freeDSP/freeDSP-CLASSIC-SMD-B/Simulations/Filter/Messungen OPA1662/NewFile0.bmp

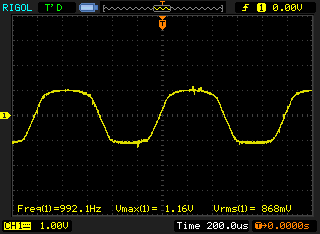
Simulations/Filter/Messungen OPA1662/NewFile0.bmp
