freeDSP/freeDSP-CLASSIC-SMD-B/Simulations/muting/measurements/inverter_freq_voltage.bmp

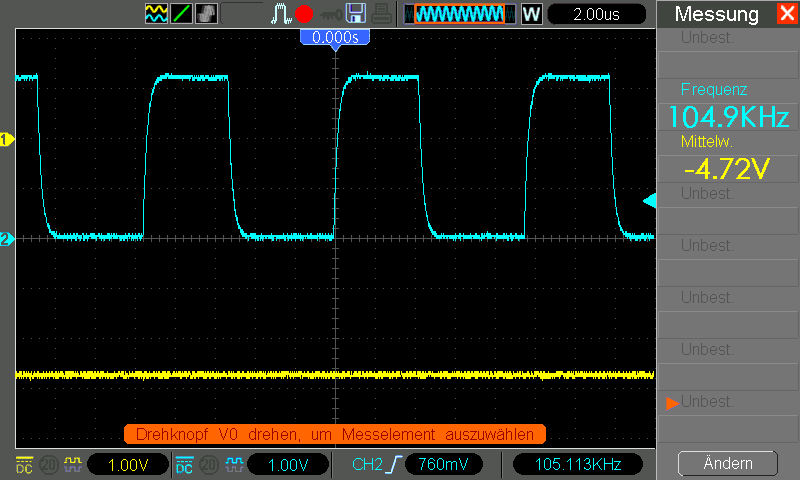
Simulations/muting/measurements/inverter_freq_voltage.bmp
