freeDSP/freeDSP-CLASSIC-SMD-B/Simulations/muting/inverter.asc

A1: schmtinv; vhigh=3.3 ref=1.5 Trise=5n Tfall=5n Td=5n
A2: schmtinv; vhigh=3.3 ref=1.5 Trise=5n Tfall=5n Td=5n
A3: schmtinv; vhigh=3.3 ref=1.5 Trise=5n Tfall=5n Td=5n
C1: cap; 100n
C2: cap; 100n
C3: cap; 100n
C4: cap; 100n
C5: cap; 10n
D1: diode; 1N4148
D2: diode; 1N4148
D3: diode; 1N4148
D4: diode; 1N4148
R1: res; 1k
R2: res; 5meg
R3: res; 1k
Named nets: 0
.tran 0 220u 200u 1u uic
Inverter sind SN74LVC3G14
f_s (gemessen) = 105kHz
