freeDSP/freeDSP-CLASSIC-SMD-B/Simulations/muting/muting.asc

C1: cap; 10µ
J1: njf; PN5434
M1: nmos; BSH103
M4: nmos; BSH103
R1: res; 10k
V1: voltage; PULSE(0 1.65 1m 5u)
V2: voltage; PULSE(0 -4 5m 5n 5n 5m)
V3: voltage; PULSE(0 3.3 5m 100u 5n 5m)
V4: voltage; SINE(1.65 1.27 1k 0 0 0)
Named nets: 0
.tran 0 10m 0 10n
.include BSH103.mod
.four 1k 10 10 v(n005)
Muting mit 0V an allen Gates, Unmuting mit 3.3V an den MOSFETs und <-4V am JFET
.include PN5434.mod
PN5434 ist abgekündigt, Ersatztyp ist MMBF5434
