freeDSP/freeDSP-CLASSIC-SMD-B/Simulations/muting/trigger.asc

C1: cap; 2.2µ
D2: diode; 1N4148
R1: res; 10k
R2: res; 10k
R3: res; 390k
R4: res; 1k
R5: res; 1meg
R6: res; 1k
U1: opamp2; LM339
V1: voltage; PULSE(0 3.3 0 5n 5n 1 1.1)
Named nets: 0, OUT
.tran 0 8 0 10u startup
Schaltet real bei ca. 500ms
.include LM339.lib
Komparator wird später ein LM393 verwendet (gleiches Verhalten wie LM339)
