freeDSP/freeDSP-CLASSIC-SMD-B/Simulations/Filter/120kHz Grenzfrequenz/120kHz.asc

C1: cap; 100p
C2: cap; 330p
C3: cap; 4.7µ
C4: cap; 4.7µ
C5: cap; 560p
R1: res; 2k
R2: res; 16k
R3: res; 2.4k
R4: res; 10k
U1: opamp2; OPA388
V1: voltage; 1.65; AC 1.27 0
V2: voltage; 3.3
V3: voltage; 3.3
Named nets: 0, V+, V-
.LIB OPA4353.lib
.LIB ad8608.cir
.ac dec 1000 1 100G
.LIB OPA1662.lib
.LIB lme49721.lib
.LIB OPA1664.lib
.LIB OPA388.txt
