freeDSP/freeDSP-CLASSIC-SMD-B/SOURCES/freeDSP_Classic_SMD.kicad_pcb

## KiCad design SOURCES/freeDSP_Classic_SMD.kicad_pcb (2019-07-08)

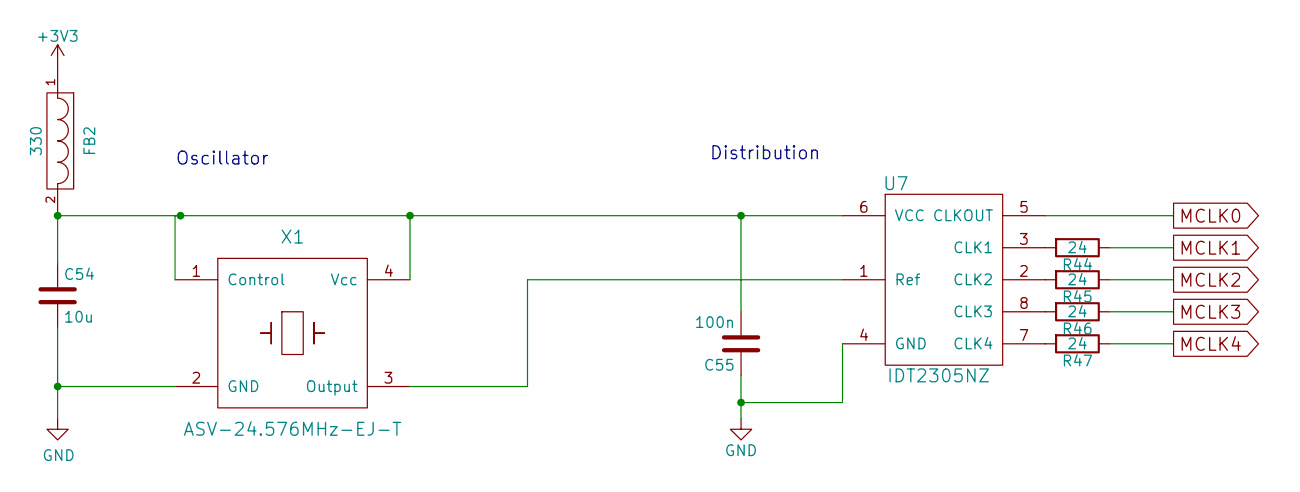
[picture p16: schematic clock-2019-01-28-18-36-09.sch, Clock]

Parts:
C54: 10u; C_1206_HandSoldering
C55: 100n; C_1206_HandSoldering
FB2: 330; C_0805_HandSoldering
R44, R45, R46, R47: 24; R_1206_HandSoldering
U7: IDT2305NZ; SOIC-8_3.9x4.9mm_Pitch1.27mm
X1: ASV-24.576MHz-EJ-T; Oscillator_SMD_Abracon_ASV-4pin_7.0x5.1mm_HandSoldering

Connections:
GND: C54.2, C55.1, U7.4 (GND), X1.2 (GND); also elsewhere on the board
MCLK0: U7.5 (CLKOUT); also elsewhere on the board
MCLK1: R44.1; also elsewhere on the board
MCLK2: R45.1; also elsewhere on the board
MCLK3: R46.1; also elsewhere on the board
MCLK4: R47.1; also elsewhere on the board
unnamed: C54.1, C55.2, FB2.2, U7.6 (VCC), X1.1 (Control), X1.4 (Vcc)
unnamed: R44.2, U7.3 (CLK1)
unnamed: R45.2, U7.2 (CLK2)
unnamed: R46.2, U7.8 (CLK3)
unnamed: R47.2, U7.7 (CLK4)
unnamed: U7.1 (Ref), X1.3 (Output)

Notes on the sheet:
Oscillator
Distribution


Parts:
C54: 10u; C_1206_HandSoldering
C55: 100n; C_1206_HandSoldering
FB2: 330; C_0805_HandSoldering
R44, R45, R46, R47: 24; R_1206_HandSoldering
U7: IDT2305NZ; SOIC-8_3.9x4.9mm_Pitch1.27mm
X1: ASV-24.576MHz-EJ-T; Oscillator_SMD_Abracon_ASV-4pin_7.0x5.1mm_HandSoldering

Connections:
GND: C54.2, C55.1, U7.4 (GND), X1.2 (GND); also elsewhere on the board
MCLK0: U7.5 (CLKOUT); also elsewhere on the board
MCLK1: R44.1; also elsewhere on the board
MCLK2: R45.1; also elsewhere on the board
MCLK3: R46.1; also elsewhere on the board
MCLK4: R47.1; also elsewhere on the board
unnamed: C54.1, C55.2, FB2.2, U7.6 (VCC), X1.1 (Control), X1.4 (Vcc)
unnamed: R44.2, U7.3 (CLK1)
unnamed: R45.2, U7.2 (CLK2)
unnamed: R46.2, U7.8 (CLK3)
unnamed: R47.2, U7.7 (CLK4)
unnamed: U7.1 (Ref), X1.3 (Output)

Notes on the sheet:
Oscillator
Distribution


Parts:
C54: 10u; C_1206_HandSoldering
C55: 100n; C_1206_HandSoldering
FB2: 330; C_0805_HandSoldering
R44, R45, R46, R47: 24; R_1206_HandSoldering
U7: IDT2305NZ; SOIC-8_3.9x4.9mm_Pitch1.27mm
X1: ASV-24.576MHz-EJ-T; Oscillator_SMD_Abracon_ASV-4pin_7.0x5.1mm_HandSoldering

Connections:
GND: C54.2, C55.1, U7.4 (GND), X1.2 (GND); also elsewhere on the board
MCLK0: U7.5 (CLKOUT); also elsewhere on the board
MCLK1: R44.1; also elsewhere on the board
MCLK2: R45.1; also elsewhere on the board
MCLK3: R46.1; also elsewhere on the board
MCLK4: R47.1; also elsewhere on the board
unnamed: C54.1, C55.2, FB2.2, U7.6 (VCC), X1.1 (Control), X1.4 (Vcc)
unnamed: R44.2, U7.3 (CLK1)
unnamed: R45.2, U7.2 (CLK2)
unnamed: R46.2, U7.8 (CLK3)
unnamed: R47.2, U7.7 (CLK4)
unnamed: U7.1 (Ref), X1.3 (Output)

Notes on the sheet:
Oscillator
Distribution

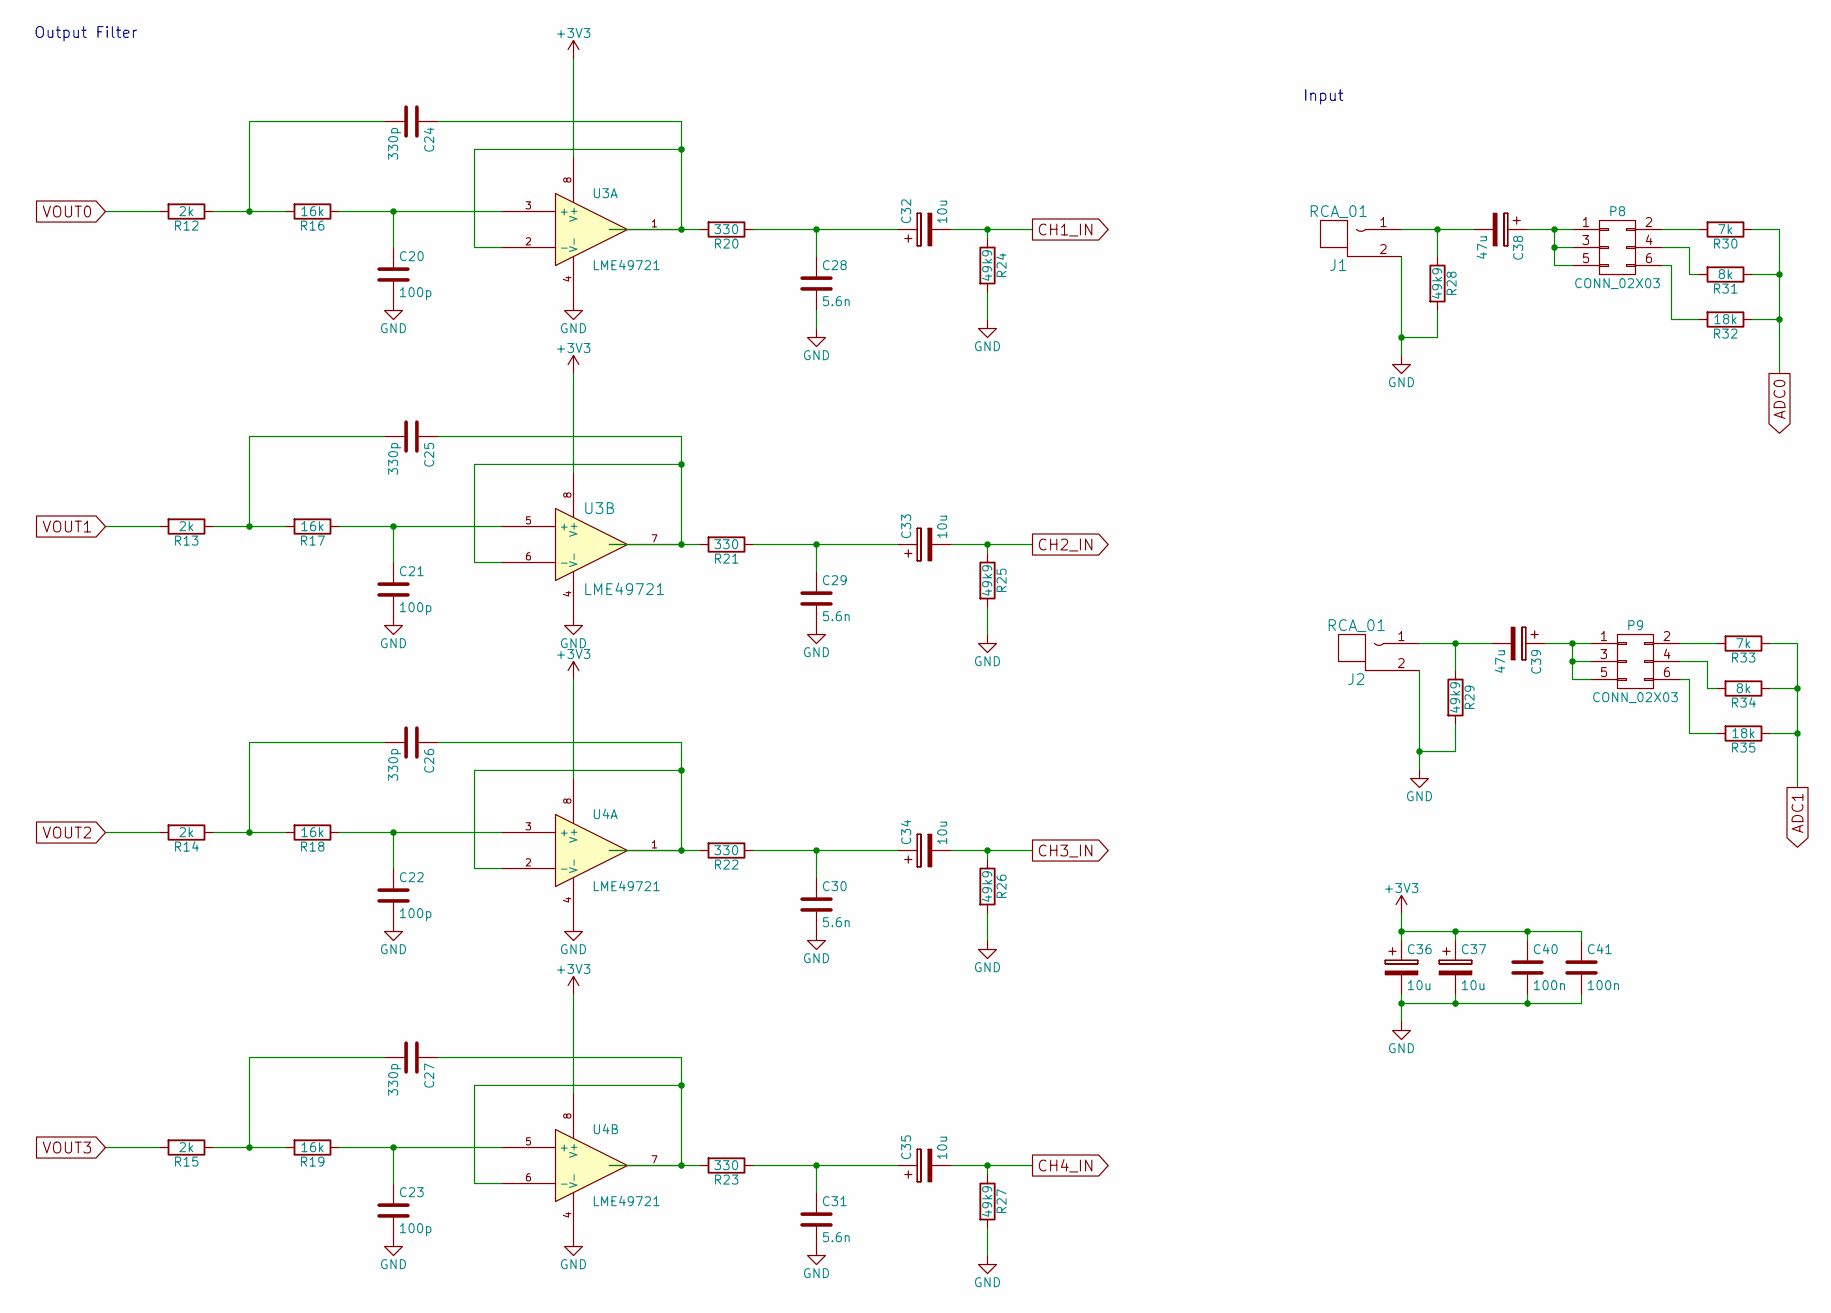
[picture p17: schematic filter-2019-01-28-18-36-09.sch, Filter]

Parts:
C20, C21, C22, C23: 100p; C_1206_HandSoldering
C24, C25, C26, C27: 330p; C_1206_HandSoldering
C28, C29, C30, C31: 5.6n; C_1206_HandSoldering
C32, C33, C34, C35, C36, C37: 10u; C_Radial_D5_L11_P2
C38, C39: 47u; C_Radial_D5_L11_P2
C40, C41: 100n; C_1206_HandSoldering
J1, J2: RCA_01; RCA_RCJ-01x
P8, P9: CONN_02X03; Pin_Header_Straight_2x03
R12, R13, R14, R15: 2k; R_1206_HandSoldering
R16, R17, R18, R19: 16k; R_1206_HandSoldering
R20, R21, R22, R23: 330; R_1206_HandSoldering
R24, R25, R26, R27, R28, R29: 49k9; R_1206_HandSoldering
R30, R33: 7k; R_1206_HandSoldering
R31, R34: 8k; R_1206_HandSoldering
R32, R35: 18k; R_1206_HandSoldering
U3, U4: LME49721; SOIC-8_3.9x4.9mm_Pitch1.27mm

Connections:
ADC0: R30.1, R31.1, R32.1; also elsewhere on the board
ADC1: R33.1, R34.1, R35.1; also elsewhere on the board
CH1_IN: C32.2, R24.1; also elsewhere on the board
CH2_IN: C33.2, R25.1; also elsewhere on the board
CH3_IN: C34.2, R26.1; also elsewhere on the board
CH4_IN: C35.2, R27.1; also elsewhere on the board
GND: C20.2, C21.2, C22.2, C23.2, C28.2, C29.2, C30.2, C31.2, C36.2, C37.2, C40.2, C41.2, J1.2 (GND), J2.2 (GND), R24.2, R25.2, R26.2, R27.2, R28.2, R29.2, U3.4 (V-), U4.4 (V-); also elsewhere on the board
unnamed: C20.1, R16.1, U3.3 (+)
unnamed: C21.1, R17.1, U3.5 (+)
unnamed: C22.1, R18.1, U4.3 (+)
unnamed: C23.1, R19.1, U4.5 (+)
unnamed: C24.1, R20.2, U3.1, U3.2 (-)
unnamed: C24.2, R12.1, R16.2
unnamed: C25.1, R21.2, U3.6 (-), U3.7
unnamed: C25.2, R13.1, R17.2
unnamed: C26.1, R22.2, U4.1, U4.2 (-)
unnamed: C26.2, R14.1, R18.2
unnamed: C27.1, R23.2, U4.6 (-), U4.7
unnamed: C27.2, R15.1, R19.2
unnamed: C28.1, C32.1, R20.1
unnamed: C29.1, C33.1, R21.1
unnamed: C30.1, C34.1, R22.1
unnamed: C31.1, C35.1, R23.1
unnamed: C38.1, P8.1, P8.3, P8.5
unnamed: C38.2, J1.1 (SIG), R28.1
unnamed: C39.1, P9.1, P9.3, P9.5
unnamed: C39.2, J2.1 (SIG), R29.1
unnamed: P8.2, R30.2
unnamed: P8.4, R31.2
unnamed: P8.6, R32.2
unnamed: P9.2, R33.2
unnamed: P9.4, R34.2
unnamed: P9.6, R35.2
VOUT0: R12.2; also elsewhere on the board
VOUT1: R13.2; also elsewhere on the board
VOUT2: R14.2; also elsewhere on the board
VOUT3: R15.2; also elsewhere on the board

Notes on the sheet:
Output Filter
Input


Parts:
C20, C21, C22, C23: 100p; C_1206_HandSoldering
C24, C25, C26, C27: 330p; C_1206_HandSoldering
C28, C29, C30, C31: 5.6n; C_1206_HandSoldering
C32, C33, C34, C35, C36, C37: 10u; C_Radial_D5_L11_P2
C38, C39: 47u; C_Radial_D5_L11_P2
C40, C41: 100n; C_1206_HandSoldering
J1, J2: RCA_01; RCA_RCJ-01x
P8, P9: CONN_02X03; Pin_Header_Straight_2x03
R12, R13, R14, R15: 2k; R_1206_HandSoldering
R16, R17, R18, R19: 16k; R_1206_HandSoldering
R20, R21, R22, R23: 330; R_1206_HandSoldering
R24, R25, R26, R27, R28, R29: 49k9; R_1206_HandSoldering
R30, R33: 7k; R_1206_HandSoldering
R31, R34: 8k; R_1206_HandSoldering
R32, R35: 18k; R_1206_HandSoldering
U3, U4: LME49721; SOIC-8_3.9x4.9mm_Pitch1.27mm

Connections:
ADC0: R30.1, R31.1, R32.1; also elsewhere on the board
ADC1: R33.1, R34.1, R35.1; also elsewhere on the board
CH1_IN: C32.2, R24.1; also elsewhere on the board
CH2_IN: C33.2, R25.1; also elsewhere on the board
CH3_IN: C34.2, R26.1; also elsewhere on the board
CH4_IN: C35.2, R27.1; also elsewhere on the board
GND: C20.2, C21.2, C22.2, C23.2, C28.2, C29.2, C30.2, C31.2, C36.2, C37.2, C40.2, C41.2, J1.2 (GND), J2.2 (GND), R24.2, R25.2, R26.2, R27.2, R28.2, R29.2, U3.4 (V-), U4.4 (V-); also elsewhere on the board
unnamed: C20.1, R16.1, U3.3 (+)
unnamed: C21.1, R17.1, U3.5 (+)
unnamed: C22.1, R18.1, U4.3 (+)
unnamed: C23.1, R19.1, U4.5 (+)
unnamed: C24.1, R20.2, U3.1, U3.2 (-)
unnamed: C24.2, R12.1, R16.2
unnamed: C25.1, R21.2, U3.6 (-), U3.7
unnamed: C25.2, R13.1, R17.2
unnamed: C26.1, R22.2, U4.1, U4.2 (-)
unnamed: C26.2, R14.1, R18.2
unnamed: C27.1, R23.2, U4.6 (-), U4.7
unnamed: C27.2, R15.1, R19.2
unnamed: C28.1, C32.1, R20.1
unnamed: C29.1, C33.1, R21.1
unnamed: C30.1, C34.1, R22.1
unnamed: C31.1, C35.1, R23.1
unnamed: C38.1, P8.1, P8.3, P8.5
unnamed: C38.2, J1.1 (SIG), R28.1
unnamed: C39.1, P9.1, P9.3, P9.5
unnamed: C39.2, J2.1 (SIG), R29.1
unnamed: P8.2, R30.2
unnamed: P8.4, R31.2
unnamed: P8.6, R32.2
unnamed: P9.2, R33.2
unnamed: P9.4, R34.2
unnamed: P9.6, R35.2
VOUT0: R12.2; also elsewhere on the board
VOUT1: R13.2; also elsewhere on the board
VOUT2: R14.2; also elsewhere on the board
VOUT3: R15.2; also elsewhere on the board

Notes on the sheet:
Output Filter
Input


Parts:
C20, C21, C22, C23: 100p; C_1206_HandSoldering
C24, C25, C26, C27: 330p; C_1206_HandSoldering
C28, C29, C30, C31: 5.6n; C_1206_HandSoldering
C32, C33, C34, C35, C36, C37: 10u; C_Radial_D5_L11_P2
C38, C39: 47u; C_Radial_D5_L11_P2
C40, C41: 100n; C_1206_HandSoldering
J1, J2: RCA_01; RCA_RCJ-01x
P8, P9: CONN_02X03; Pin_Header_Straight_2x03
R12, R13, R14, R15: 2k; R_1206_HandSoldering
R16, R17, R18, R19: 16k; R_1206_HandSoldering
R20, R21, R22, R23: 330; R_1206_HandSoldering
R24, R25, R26, R27, R28, R29: 49k9; R_1206_HandSoldering
R30, R33: 7k; R_1206_HandSoldering
R31, R34: 8k; R_1206_HandSoldering
R32, R35: 18k; R_1206_HandSoldering
U3, U4: LME49721; SOIC-8_3.9x4.9mm_Pitch1.27mm

Connections:
ADC0: R30.1, R31.1, R32.1; also elsewhere on the board
ADC1: R33.1, R34.1, R35.1; also elsewhere on the board
CH1_IN: C32.2, R24.1; also elsewhere on the board
CH2_IN: C33.2, R25.1; also elsewhere on the board
CH3_IN: C34.2, R26.1; also elsewhere on the board
CH4_IN: C35.2, R27.1; also elsewhere on the board
GND: C20.2, C21.2, C22.2, C23.2, C28.2, C29.2, C30.2, C31.2, C36.2, C37.2, C40.2, C41.2, J1.2 (GND), J2.2 (GND), R24.2, R25.2, R26.2, R27.2, R28.2, R29.2, U3.4 (V-), U4.4 (V-); also elsewhere on the board
unnamed: C20.1, R16.1, U3.3 (+)
unnamed: C21.1, R17.1, U3.5 (+)
unnamed: C22.1, R18.1, U4.3 (+)
unnamed: C23.1, R19.1, U4.5 (+)
unnamed: C24.1, R20.2, U3.1, U3.2 (-)
unnamed: C24.2, R12.1, R16.2
unnamed: C25.1, R21.2, U3.6 (-), U3.7
unnamed: C25.2, R13.1, R17.2
unnamed: C26.1, R22.2, U4.1, U4.2 (-)
unnamed: C26.2, R14.1, R18.2
unnamed: C27.1, R23.2, U4.6 (-), U4.7
unnamed: C27.2, R15.1, R19.2
unnamed: C28.1, C32.1, R20.1
unnamed: C29.1, C33.1, R21.1
unnamed: C30.1, C34.1, R22.1
unnamed: C31.1, C35.1, R23.1
unnamed: C38.1, P8.1, P8.3, P8.5
unnamed: C38.2, J1.1 (SIG), R28.1
unnamed: C39.1, P9.1, P9.3, P9.5
unnamed: C39.2, J2.1 (SIG), R29.1
unnamed: P8.2, R30.2
unnamed: P8.4, R31.2
unnamed: P8.6, R32.2
unnamed: P9.2, R33.2
unnamed: P9.4, R34.2
unnamed: P9.6, R35.2
VOUT0: R12.2; also elsewhere on the board
VOUT1: R13.2; also elsewhere on the board
VOUT2: R14.2; also elsewhere on the board
VOUT3: R15.2; also elsewhere on the board

Notes on the sheet:
Output Filter
Input

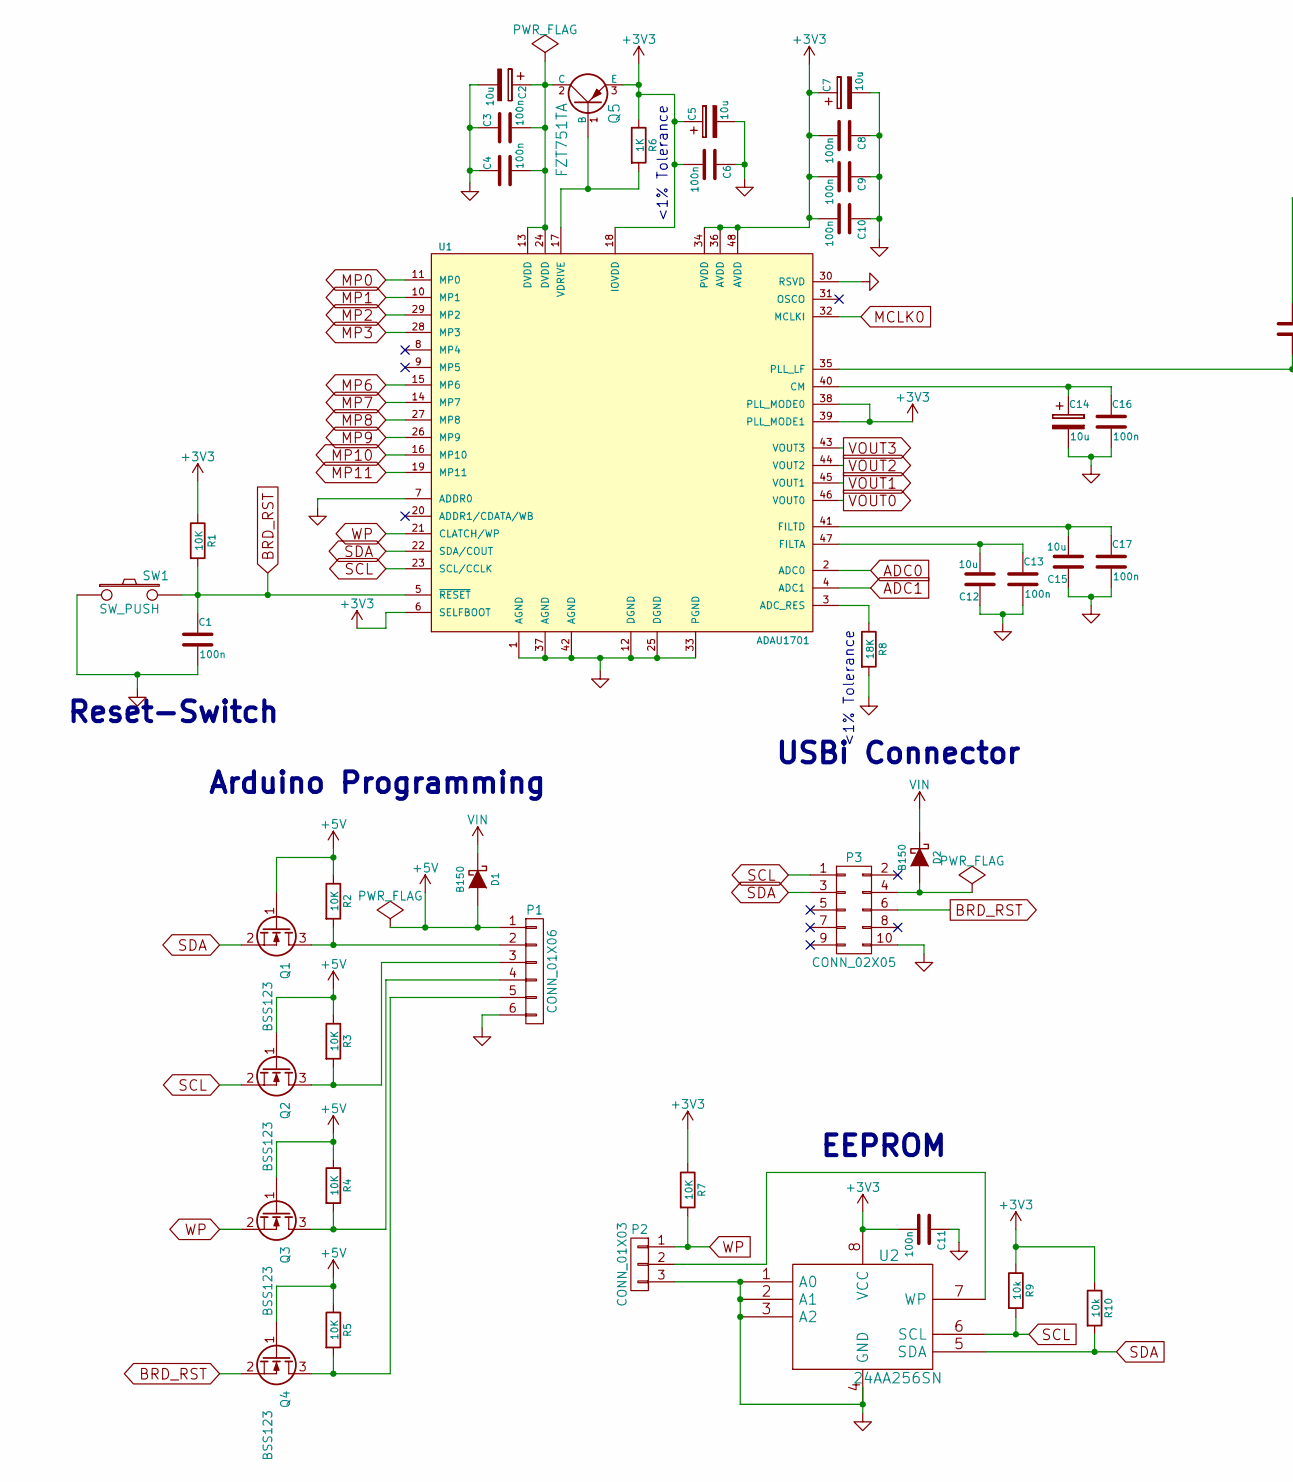
[picture p18: schematic freeDSP_Classic_SMD-2019-01-28-18-36-09.sch, freeDSP Classic SMD, part in row 1, column 1]

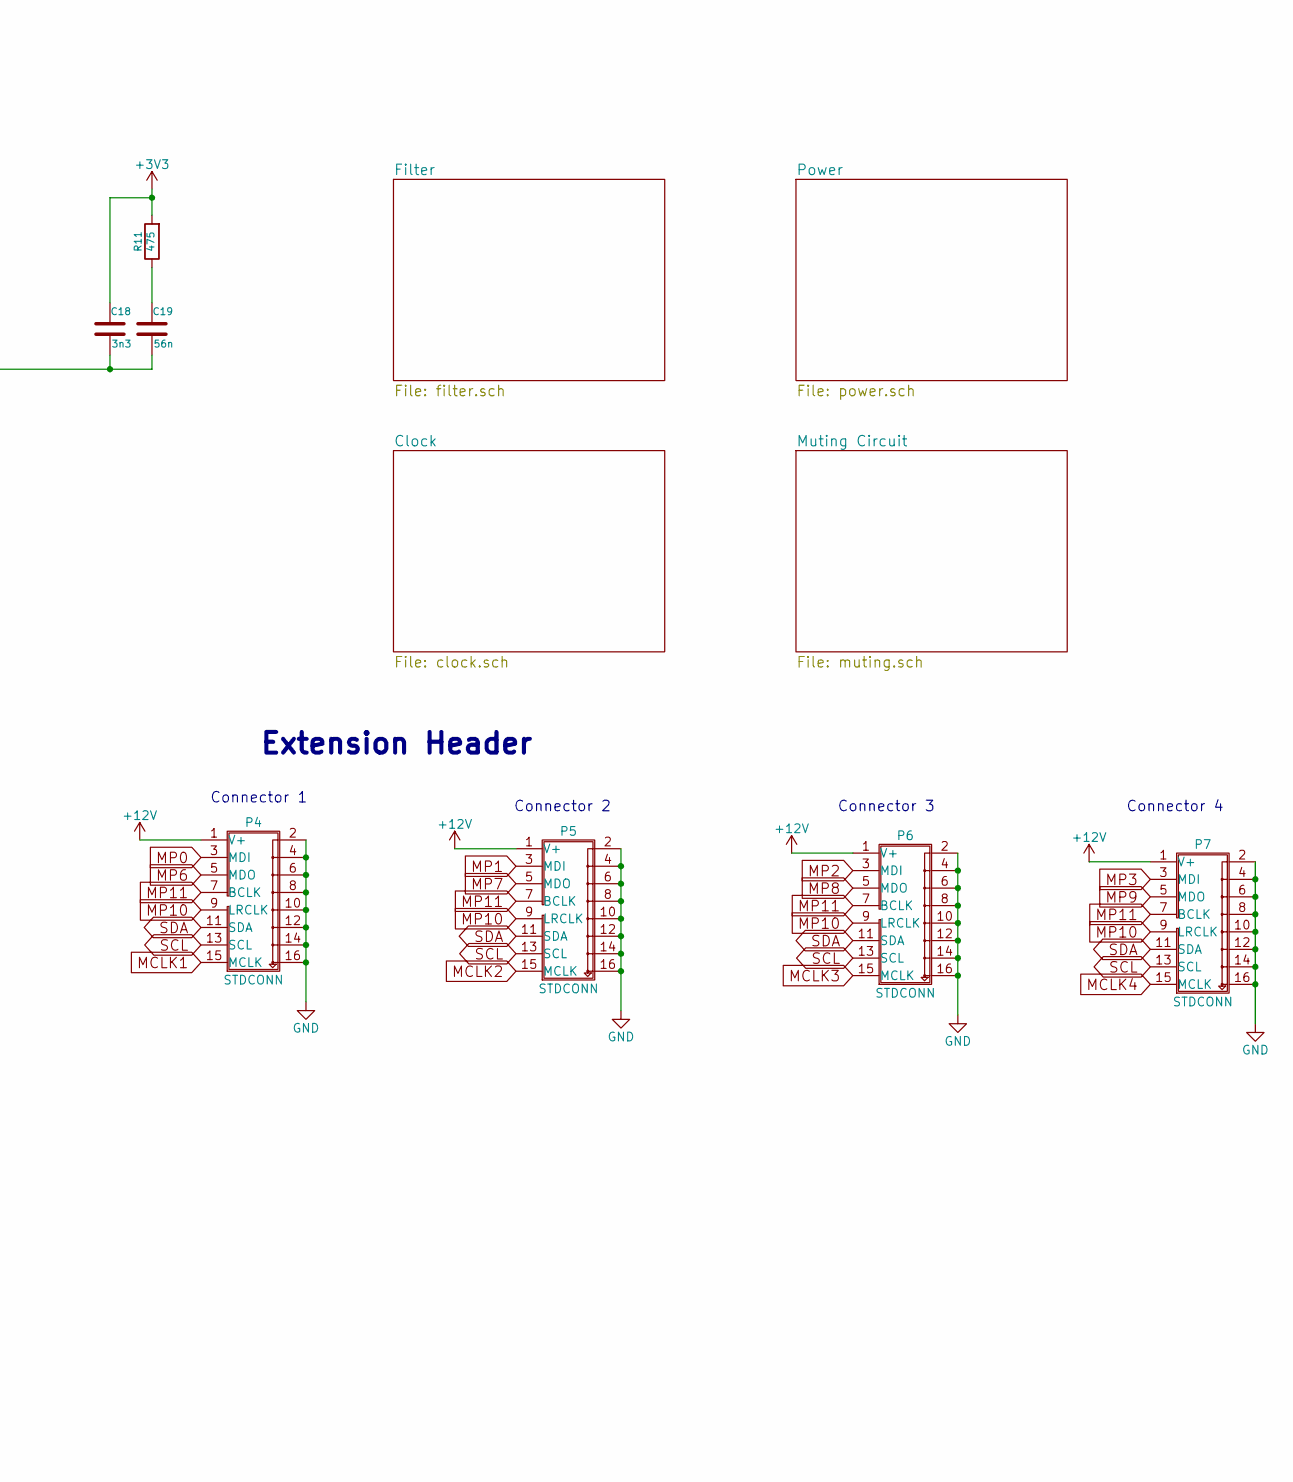
[picture p19: schematic freeDSP_Classic_SMD-2019-01-28-18-36-09.sch, freeDSP Classic SMD, part in row 1, column 2]

Parts:
C1, C3, C4, C6, C8, C9, C10, C11, C13, C16, C17: 100n; C_1206_HandSoldering
C2, C5, C7, C14: 10u; C_Radial_D5_L11_P2
C12, C15: 10u; C_1206_HandSoldering
C18: 3n3; C_1206_HandSoldering
C19: 56n; C_1206_HandSoldering
D1, D2: B150; SMA
P1: CONN_01X06; Pin_Header_Straight_1x06
P2: CONN_01X03; Pin_Header_Straight_1x03
P3: CONN_02X05; IDC_Header_Straight_10pins
P4, P5, P6, P7: STDCONN; IDC_Header_Straight_16pins
Q1, Q2, Q3, Q4: BSS123; SOT-23_Handsoldering
Q5: FZT751TA; SOT-223
R1, R2, R3, R4, R5, R7: 10K; R_1206_HandSoldering
R6: 1K; R_1206_HandSoldering
R8: 18K; R_1206_HandSoldering
R9, R10: 10k; R_1206_HandSoldering
R11: 475; R_1206_HandSoldering
SW1: SW_PUSH; SW_PUSH_6mm
U1: ADAU1701; LQFP-48_7x7mm_Pitch0.5mm
U2: 24AA256SN; SOIC-8_3.9x4.9mm_Pitch1.27mm

Connections:
+5V: D1.2 (A), P1.1, Q1.1 (G), Q2.1 (G), Q3.1 (G), Q4.1 (G), R2.1, R3.1, R4.1, R5.1
+12V: P4.1 (V+), P5.1 (V+), P6.1 (V+), P7.1 (V+); also elsewhere on the board
ADC0: U1.2 (ADC0); also elsewhere on the board
ADC1: U1.4 (ADC1); also elsewhere on the board
BRD_RST: C1.1, P3.6, Q4.2 (S), R1.2, SW1.2, U1.5 (~RESET~)
GND: C1.2, C2.2, C3.1, C4.1, C5.2, C6.1, C7.2, C8.1, C9.1, C10.1, C11.1, C12.1, C13.2, C14.2, C15.1, C16.2, C17.2, P1.6, P2.3, P3.10, P4.2 (GND), P4.4 (GND), P4.6 (GND), P4.8 (GND), P4.10 (GND), P4.12 (GND), P4.14 (GND), P4.16 (GND), P5.2 (GND), P5.4 (GND), P5.6 (GND), P5.8 (GND), P5.10 (GND), P5.12 (GND), P5.14 (GND), P5.16 (GND), P6.2 (GND), P6.4 (GND), P6.6 (GND), P6.8 (GND), P6.10 (GND), P6.12 (GND), P6.14 (GND), P6.16 (GND), P7.2 (GND), P7.4 (GND), P7.6 (GND), P7.8 (GND), P7.10 (GND), P7.12 (GND), P7.14 (GND), P7.16 (GND), R8.2, SW1.1, U1.1 (AGND), U1.7 (ADDR0), U1.12 (DGND), U1.25 (DGND), U1.30 (RSVD), U1.33 (PGND), U1.37 (AGND), U1.42 (AGND), U2.1 (A0), U2.2 (A1), U2.3 (A2), U2.4 (GND); also elsewhere on the board
MCLK0: U1.32 (MCLKI); also elsewhere on the board
MCLK1: P4.15 (MCLK); also elsewhere on the board
MCLK2: P5.15 (MCLK); also elsewhere on the board
MCLK3: P6.15 (MCLK); also elsewhere on the board
MCLK4: P7.15 (MCLK); also elsewhere on the board
MP0: P4.3 (MDI), U1.11 (MP0)
MP1: P5.3 (MDI), U1.10 (MP1)
MP2: P6.3 (MDI), U1.29 (MP2)
MP3: P7.3 (MDI), U1.28 (MP3)
MP4: U1.8 (MP4); also elsewhere on the board
MP5: U1.9 (MP5); also elsewhere on the board
MP6: P4.5 (MDO), U1.15 (MP6)
MP7: P5.5 (MDO), U1.14 (MP7)
MP8: P6.5 (MDO), U1.27 (MP8)
MP9: P7.5 (MDO), U1.26 (MP9)
unnamed: C2.1, C3.2, C4.2, Q5.2 (C), U1.13 (DVDD), U1.24 (DVDD)
unnamed: C12.2, C13.1, U1.47 (FILTA)
unnamed: C14.1, C16.1, U1.40 (CM)
unnamed: C15.2, C17.1, U1.41 (FILTD)
unnamed: C18.2, C19.2, U1.35 (PLL_LF)
unnamed: C19.1, R11.1
unnamed: D2.2 (A), P3.4
unnamed: P1.2, Q1.3 (D), R2.2
unnamed: P1.3, Q2.3 (D), R3.2
unnamed: P1.4, Q3.3 (D), R4.2
unnamed: P1.5, Q4.3 (D), R5.2
unnamed: P2.2, U2.7 (WP)
unnamed: Q5.1 (B), R6.2, U1.17 (VDRIVE)
unnamed: R8.1, U1.3 (ADC_RES)
SCL: P3.1, P4.13 (SCL), P5.13 (SCL), P6.13 (SCL), P7.13 (SCL), Q2.2 (S), R9.2, U1.23 (SCL/CCLK), U2.6 (SCL)
SDA: P3.3, P4.11 (SDA), P5.11 (SDA), P6.11 (SDA), P7.11 (SDA), Q1.2 (S), R10.2, U1.22 (SDA/COUT), U2.5 (SDA)
VIN: D1.1 (K), D2.1 (K); also elsewhere on the board
VOUT0: U1.46 (VOUT0); also elsewhere on the board
VOUT1: U1.45 (VOUT1); also elsewhere on the board
VOUT2: U1.44 (VOUT2); also elsewhere on the board
VOUT3: U1.43 (VOUT3); also elsewhere on the board
WP: P2.1, Q3.2 (S), R7.2, U1.21 (CLATCH/WP)

Notes on the sheet:
Reset-Switch
<1% Tolerance
EEPROM
USBi Connector
Arduino Programming
Extension Header
Connector 2
Connector 3
Connector 4
Connector 1
