freeDSP/freeDSP-CLASSIC-SMD-B/SOURCES/freeDSP_Classic_SMD.kicad_pcb

## KiCad design SOURCES/freeDSP_Classic_SMD.kicad_pcb (continued)



Parts:
C1, C3, C4, C6, C8, C9, C10, C11, C13, C16, C17: 100n; C_1206_HandSoldering
C2, C5, C7, C14: 10u; C_Radial_D5_L11_P2
C12, C15: 10u; C_1206_HandSoldering
C18: 3n3; C_1206_HandSoldering
C19: 56n; C_1206_HandSoldering
D1, D2: B150; SMA
P1: CONN_01X06; Pin_Header_Straight_1x06
P2: CONN_01X03; Pin_Header_Straight_1x03
P3: CONN_02X05; IDC_Header_Straight_10pins
P4, P5, P6, P7: STDCONN; IDC_Header_Straight_16pins
Q1, Q2, Q3, Q4: BSS123; SOT-23_Handsoldering
Q5: FZT751TA; SOT-223
R1, R2, R3, R4, R5, R7: 10K; R_1206_HandSoldering
R6: 1K; R_1206_HandSoldering
R8: 18K; R_1206_HandSoldering
R9, R10: 10k; R_1206_HandSoldering
R11: 475; R_1206_HandSoldering
SW1: SW_PUSH; SW_PUSH_6mm
U1: ADAU1701; LQFP-48_7x7mm_Pitch0.5mm
U2: 24AA256SN; SOIC-8_3.9x4.9mm_Pitch1.27mm

Connections:
+5V: D1.2 (A), P1.1, Q1.1 (G), Q2.1 (G), Q3.1 (G), Q4.1 (G), R2.1, R3.1, R4.1, R5.1
+12V: P4.1 (V+), P5.1 (V+), P6.1 (V+), P7.1 (V+); also elsewhere on the board
ADC0: U1.2 (ADC0); also elsewhere on the board
ADC1: U1.4 (ADC1); also elsewhere on the board
BRD_RST: C1.1, P3.6, Q4.2 (S), R1.2, SW1.2, U1.5 (~RESET~)
GND: C1.2, C2.2, C3.1, C4.1, C5.2, C6.1, C7.2, C8.1, C9.1, C10.1, C11.1, C12.1, C13.2, C14.2, C15.1, C16.2, C17.2, P1.6, P2.3, P3.10, P4.2 (GND), P4.4 (GND), P4.6 (GND), P4.8 (GND), P4.10 (GND), P4.12 (GND), P4.14 (GND), P4.16 (GND), P5.2 (GND), P5.4 (GND), P5.6 (GND), P5.8 (GND), P5.10 (GND), P5.12 (GND), P5.14 (GND), P5.16 (GND), P6.2 (GND), P6.4 (GND), P6.6 (GND), P6.8 (GND), P6.10 (GND), P6.12 (GND), P6.14 (GND), P6.16 (GND), P7.2 (GND), P7.4 (GND), P7.6 (GND), P7.8 (GND), P7.10 (GND), P7.12 (GND), P7.14 (GND), P7.16 (GND), R8.2, SW1.1, U1.1 (AGND), U1.7 (ADDR0), U1.12 (DGND), U1.25 (DGND), U1.30 (RSVD), U1.33 (PGND), U1.37 (AGND), U1.42 (AGND), U2.1 (A0), U2.2 (A1), U2.3 (A2), U2.4 (GND); also elsewhere on the board
MCLK0: U1.32 (MCLKI); also elsewhere on the board
MCLK1: P4.15 (MCLK); also elsewhere on the board
MCLK2: P5.15 (MCLK); also elsewhere on the board
MCLK3: P6.15 (MCLK); also elsewhere on the board
MCLK4: P7.15 (MCLK); also elsewhere on the board
MP0: P4.3 (MDI), U1.11 (MP0)
MP1: P5.3 (MDI), U1.10 (MP1)
MP2: P6.3 (MDI), U1.29 (MP2)
MP3: P7.3 (MDI), U1.28 (MP3)
MP4: U1.8 (MP4); also elsewhere on the board
MP5: U1.9 (MP5); also elsewhere on the board
MP6: P4.5 (MDO), U1.15 (MP6)
MP7: P5.5 (MDO), U1.14 (MP7)
MP8: P6.5 (MDO), U1.27 (MP8)
MP9: P7.5 (MDO), U1.26 (MP9)
unnamed: C2.1, C3.2, C4.2, Q5.2 (C), U1.13 (DVDD), U1.24 (DVDD)
unnamed: C12.2, C13.1, U1.47 (FILTA)
unnamed: C14.1, C16.1, U1.40 (CM)
unnamed: C15.2, C17.1, U1.41 (FILTD)
unnamed: C18.2, C19.2, U1.35 (PLL_LF)
unnamed: C19.1, R11.1
unnamed: D2.2 (A), P3.4
unnamed: P1.2, Q1.3 (D), R2.2
unnamed: P1.3, Q2.3 (D), R3.2
unnamed: P1.4, Q3.3 (D), R4.2
unnamed: P1.5, Q4.3 (D), R5.2
unnamed: P2.2, U2.7 (WP)
unnamed: Q5.1 (B), R6.2, U1.17 (VDRIVE)
unnamed: R8.1, U1.3 (ADC_RES)
SCL: P3.1, P4.13 (SCL), P5.13 (SCL), P6.13 (SCL), P7.13 (SCL), Q2.2 (S), R9.2, U1.23 (SCL/CCLK), U2.6 (SCL)
SDA: P3.3, P4.11 (SDA), P5.11 (SDA), P6.11 (SDA), P7.11 (SDA), Q1.2 (S), R10.2, U1.22 (SDA/COUT), U2.5 (SDA)
VIN: D1.1 (K), D2.1 (K); also elsewhere on the board
VOUT0: U1.46 (VOUT0); also elsewhere on the board
VOUT1: U1.45 (VOUT1); also elsewhere on the board
VOUT2: U1.44 (VOUT2); also elsewhere on the board
VOUT3: U1.43 (VOUT3); also elsewhere on the board
WP: P2.1, Q3.2 (S), R7.2, U1.21 (CLATCH/WP)

Notes on the sheet:
Reset-Switch
<1% Tolerance
EEPROM
USBi Connector
Arduino Programming
Extension Header
Connector 2
Connector 3
Connector 4
Connector 1



Parts:
C1, C3, C4, C6, C8, C9, C10, C11, C13, C16, C17: 100n; C_1206_HandSoldering
C2, C5, C7, C14: 10u; C_Radial_D5_L11_P2
C12, C15: 10u; C_1206_HandSoldering
C18: 3n3; C_1206_HandSoldering
C19: 56n; C_1206_HandSoldering
D1, D2: B150; SMA
P1: CONN_01X06; Pin_Header_Straight_1x06
P2: CONN_01X03; Pin_Header_Straight_1x03
P3: CONN_02X05; IDC_Header_Straight_10pins
P4, P5, P6, P7: STDCONN; IDC_Header_Straight_16pins
Q1, Q2, Q3, Q4: BSS123; SOT-23_Handsoldering
Q5: FZT751TA; SOT-223
R1, R2, R3, R4, R5, R7: 10K; R_1206_HandSoldering
R6: 1K; R_1206_HandSoldering
R8: 18K; R_1206_HandSoldering
R9, R10: 10k; R_1206_HandSoldering
R11: 475; R_1206_HandSoldering
SW1: SW_PUSH; SW_PUSH_6mm
U1: ADAU1701; LQFP-48_7x7mm_Pitch0.5mm
U2: 24AA256SN; SOIC-8_3.9x4.9mm_Pitch1.27mm

Connections:
+5V: D1.2 (A), P1.1, Q1.1 (G), Q2.1 (G), Q3.1 (G), Q4.1 (G), R2.1, R3.1, R4.1, R5.1
+12V: P4.1 (V+), P5.1 (V+), P6.1 (V+), P7.1 (V+); also elsewhere on the board
ADC0: U1.2 (ADC0); also elsewhere on the board
ADC1: U1.4 (ADC1); also elsewhere on the board
BRD_RST: C1.1, P3.6, Q4.2 (S), R1.2, SW1.2, U1.5 (~RESET~)
GND: C1.2, C2.2, C3.1, C4.1, C5.2, C6.1, C7.2, C8.1, C9.1, C10.1, C11.1, C12.1, C13.2, C14.2, C15.1, C16.2, C17.2, P1.6, P2.3, P3.10, P4.2 (GND), P4.4 (GND), P4.6 (GND), P4.8 (GND), P4.10 (GND), P4.12 (GND), P4.14 (GND), P4.16 (GND), P5.2 (GND), P5.4 (GND), P5.6 (GND), P5.8 (GND), P5.10 (GND), P5.12 (GND), P5.14 (GND), P5.16 (GND), P6.2 (GND), P6.4 (GND), P6.6 (GND), P6.8 (GND), P6.10 (GND), P6.12 (GND), P6.14 (GND), P6.16 (GND), P7.2 (GND), P7.4 (GND), P7.6 (GND), P7.8 (GND), P7.10 (GND), P7.12 (GND), P7.14 (GND), P7.16 (GND), R8.2, SW1.1, U1.1 (AGND), U1.7 (ADDR0), U1.12 (DGND), U1.25 (DGND), U1.30 (RSVD), U1.33 (PGND), U1.37 (AGND), U1.42 (AGND), U2.1 (A0), U2.2 (A1), U2.3 (A2), U2.4 (GND); also elsewhere on the board
MCLK0: U1.32 (MCLKI); also elsewhere on the board
MCLK1: P4.15 (MCLK); also elsewhere on the board
MCLK2: P5.15 (MCLK); also elsewhere on the board
MCLK3: P6.15 (MCLK); also elsewhere on the board
MCLK4: P7.15 (MCLK); also elsewhere on the board
MP0: P4.3 (MDI), U1.11 (MP0)
MP1: P5.3 (MDI), U1.10 (MP1)
MP2: P6.3 (MDI), U1.29 (MP2)
MP3: P7.3 (MDI), U1.28 (MP3)
MP4: U1.8 (MP4); also elsewhere on the board
MP5: U1.9 (MP5); also elsewhere on the board
MP6: P4.5 (MDO), U1.15 (MP6)
MP7: P5.5 (MDO), U1.14 (MP7)
MP8: P6.5 (MDO), U1.27 (MP8)
MP9: P7.5 (MDO), U1.26 (MP9)
unnamed: C2.1, C3.2, C4.2, Q5.2 (C), U1.13 (DVDD), U1.24 (DVDD)
unnamed: C12.2, C13.1, U1.47 (FILTA)
unnamed: C14.1, C16.1, U1.40 (CM)
unnamed: C15.2, C17.1, U1.41 (FILTD)
unnamed: C18.2, C19.2, U1.35 (PLL_LF)
unnamed: C19.1, R11.1
unnamed: D2.2 (A), P3.4
unnamed: P1.2, Q1.3 (D), R2.2
unnamed: P1.3, Q2.3 (D), R3.2
unnamed: P1.4, Q3.3 (D), R4.2
unnamed: P1.5, Q4.3 (D), R5.2
unnamed: P2.2, U2.7 (WP)
unnamed: Q5.1 (B), R6.2, U1.17 (VDRIVE)
unnamed: R8.1, U1.3 (ADC_RES)
SCL: P3.1, P4.13 (SCL), P5.13 (SCL), P6.13 (SCL), P7.13 (SCL), Q2.2 (S), R9.2, U1.23 (SCL/CCLK), U2.6 (SCL)
SDA: P3.3, P4.11 (SDA), P5.11 (SDA), P6.11 (SDA), P7.11 (SDA), Q1.2 (S), R10.2, U1.22 (SDA/COUT), U2.5 (SDA)
VIN: D1.1 (K), D2.1 (K); also elsewhere on the board
VOUT0: U1.46 (VOUT0); also elsewhere on the board
VOUT1: U1.45 (VOUT1); also elsewhere on the board
VOUT2: U1.44 (VOUT2); also elsewhere on the board
VOUT3: U1.43 (VOUT3); also elsewhere on the board
WP: P2.1, Q3.2 (S), R7.2, U1.21 (CLATCH/WP)

Notes on the sheet:
Reset-Switch
<1% Tolerance
EEPROM
USBi Connector
Arduino Programming
Extension Header
Connector 2
Connector 3
Connector 4
Connector 1

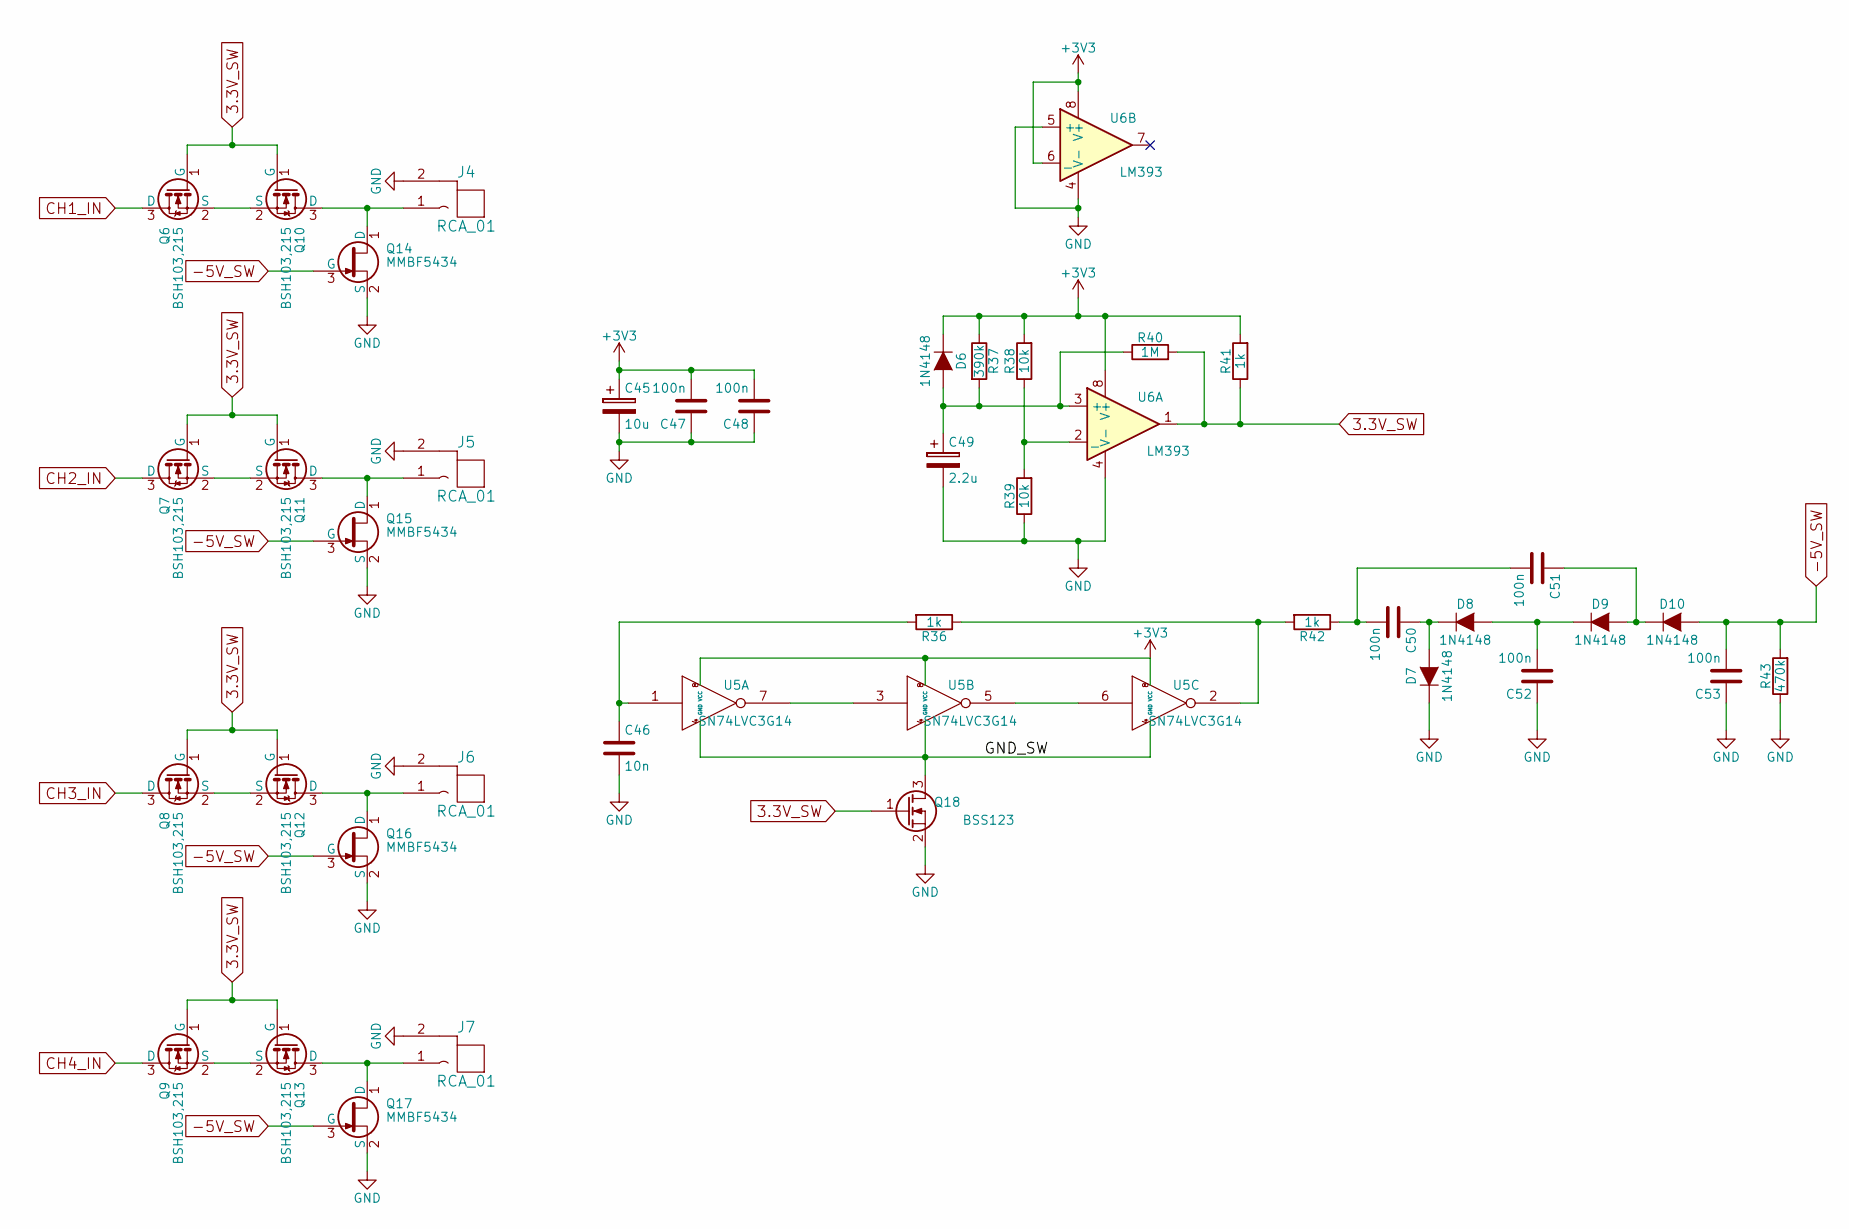
[picture p20: schematic muting-2019-01-28-18-36-09.sch, Muting]

Parts:
C45: 10u; C_Radial_D5_L11_P2
C46: 10n; C_1206_HandSoldering
C47, C48, C50, C51, C52, C53: 100n; C_1206_HandSoldering
C49: 2.2u; C_Radial_D5_L11_P2
D6, D7, D8, D9, D10: 1N4148; SOD-123W
J4, J5, J6, J7: RCA_01; RCA_RCJ-01x
Q6, Q7, Q8, Q9, Q10, Q11, Q12, Q13: BSH103,215; SOT-23_Handsoldering
Q14, Q15, Q16, Q17: MMBF5434; SOT-23_Handsoldering
Q18: BSS123; SOT-23_Handsoldering
R36, R41, R42: 1k; R_1206_HandSoldering
R37: 390k; R_1206_HandSoldering
R38, R39: 10k; R_1206_HandSoldering
R40: 1M; R_1206_HandSoldering
R43: 470k; R_1206_HandSoldering
U5: SN74LVC3G14; DCT
U6: LM393; SOIC-8_3.9x4.9mm_Pitch1.27mm

Connections:
3.3V_SW: Q6.1 (G), Q7.1 (G), Q8.1 (G), Q9.1 (G), Q10.1 (G), Q11.1 (G), Q12.1 (G), Q13.1 (G), Q18.1 (G), R40.2, R41.1, U6.1
-5V_SW: C53.2, D10.2 (A), Q14.3 (G), Q15.3 (G), Q16.3 (G), Q17.3 (G), R43.2
/Muting Circuit/GND_SW: Q18.3 (D), U5.4 (GND)
CH1_IN: Q6.3 (D); also elsewhere on the board
CH2_IN: Q7.3 (D); also elsewhere on the board
CH3_IN: Q8.3 (D); also elsewhere on the board
CH4_IN: Q9.3 (D); also elsewhere on the board
GND: C45.2, C46.2, C47.1, C48.1, C49.2, C52.1, C53.1, D7.1 (K), J4.2 (GND), J5.2 (GND), J6.2 (GND), J7.2 (GND), Q14.2 (S), Q15.2 (S), Q16.2 (S), Q17.2 (S), Q18.2 (S), R39.1, R43.1, U6.4 (V-), U6.5 (+); also elsewhere on the board
unnamed: C46.1, R36.2, U5.1
unnamed: C49.1, D6.2 (A), R37.2, R40.1, U6.3 (+)
unnamed: C50.1, D7.2 (A), D8.1 (K)
unnamed: C50.2, C51.2, R42.1
unnamed: C51.1, D9.2 (A), D10.1 (K)
unnamed: C52.2, D8.2 (A), D9.1 (K)
unnamed: J4.1 (SIG), Q10.3 (D), Q14.1 (D)
unnamed: J5.1 (SIG), Q11.3 (D), Q15.1 (D)
unnamed: J6.1 (SIG), Q12.3 (D), Q16.1 (D)
unnamed: J7.1 (SIG), Q13.3 (D), Q17.1 (D)
unnamed: Q6.2 (S), Q10.2 (S)
unnamed: Q7.2 (S), Q11.2 (S)
unnamed: Q8.2 (S), Q12.2 (S)
unnamed: Q9.2 (S), Q13.2 (S)
unnamed: R36.1, R42.2, U5.2
unnamed: R38.1, R39.2, U6.2 (_)
unnamed: U5.3, U5.7
unnamed: U5.5, U5.6


Parts:
C45: 10u; C_Radial_D5_L11_P2
C46: 10n; C_1206_HandSoldering
C47, C48, C50, C51, C52, C53: 100n; C_1206_HandSoldering
C49: 2.2u; C_Radial_D5_L11_P2
D6, D7, D8, D9, D10: 1N4148; SOD-123W
J4, J5, J6, J7: RCA_01; RCA_RCJ-01x
Q6, Q7, Q8, Q9, Q10, Q11, Q12, Q13: BSH103,215; SOT-23_Handsoldering
Q14, Q15, Q16, Q17: MMBF5434; SOT-23_Handsoldering
Q18: BSS123; SOT-23_Handsoldering
R36, R41, R42: 1k; R_1206_HandSoldering
R37: 390k; R_1206_HandSoldering
R38, R39: 10k; R_1206_HandSoldering
R40: 1M; R_1206_HandSoldering
R43: 470k; R_1206_HandSoldering
U5: SN74LVC3G14; DCT
U6: LM393; SOIC-8_3.9x4.9mm_Pitch1.27mm

Connections:
3.3V_SW: Q6.1 (G), Q7.1 (G), Q8.1 (G), Q9.1 (G), Q10.1 (G), Q11.1 (G), Q12.1 (G), Q13.1 (G), Q18.1 (G), R40.2, R41.1, U6.1
-5V_SW: C53.2, D10.2 (A), Q14.3 (G), Q15.3 (G), Q16.3 (G), Q17.3 (G), R43.2
/Muting Circuit/GND_SW: Q18.3 (D), U5.4 (GND)
CH1_IN: Q6.3 (D); also elsewhere on the board
CH2_IN: Q7.3 (D); also elsewhere on the board
CH3_IN: Q8.3 (D); also elsewhere on the board
CH4_IN: Q9.3 (D); also elsewhere on the board
GND: C45.2, C46.2, C47.1, C48.1, C49.2, C52.1, C53.1, D7.1 (K), J4.2 (GND), J5.2 (GND), J6.2 (GND), J7.2 (GND), Q14.2 (S), Q15.2 (S), Q16.2 (S), Q17.2 (S), Q18.2 (S), R39.1, R43.1, U6.4 (V-), U6.5 (+); also elsewhere on the board
unnamed: C46.1, R36.2, U5.1
unnamed: C49.1, D6.2 (A), R37.2, R40.1, U6.3 (+)
unnamed: C50.1, D7.2 (A), D8.1 (K)
unnamed: C50.2, C51.2, R42.1
unnamed: C51.1, D9.2 (A), D10.1 (K)
unnamed: C52.2, D8.2 (A), D9.1 (K)
unnamed: J4.1 (SIG), Q10.3 (D), Q14.1 (D)
unnamed: J5.1 (SIG), Q11.3 (D), Q15.1 (D)
unnamed: J6.1 (SIG), Q12.3 (D), Q16.1 (D)
unnamed: J7.1 (SIG), Q13.3 (D), Q17.1 (D)
unnamed: Q6.2 (S), Q10.2 (S)
unnamed: Q7.2 (S), Q11.2 (S)
unnamed: Q8.2 (S), Q12.2 (S)
unnamed: Q9.2 (S), Q13.2 (S)
unnamed: R36.1, R42.2, U5.2
unnamed: R38.1, R39.2, U6.2 (_)
unnamed: U5.3, U5.7
unnamed: U5.5, U5.6


Parts:
C45: 10u; C_Radial_D5_L11_P2
C46: 10n; C_1206_HandSoldering
C47, C48, C50, C51, C52, C53: 100n; C_1206_HandSoldering
C49: 2.2u; C_Radial_D5_L11_P2
D6, D7, D8, D9, D10: 1N4148; SOD-123W
J4, J5, J6, J7: RCA_01; RCA_RCJ-01x
Q6, Q7, Q8, Q9, Q10, Q11, Q12, Q13: BSH103,215; SOT-23_Handsoldering
Q14, Q15, Q16, Q17: MMBF5434; SOT-23_Handsoldering
Q18: BSS123; SOT-23_Handsoldering
R36, R41, R42: 1k; R_1206_HandSoldering
R37: 390k; R_1206_HandSoldering
R38, R39: 10k; R_1206_HandSoldering
R40: 1M; R_1206_HandSoldering
R43: 470k; R_1206_HandSoldering
U5: SN74LVC3G14; DCT
U6: LM393; SOIC-8_3.9x4.9mm_Pitch1.27mm

Connections:
3.3V_SW: Q6.1 (G), Q7.1 (G), Q8.1 (G), Q9.1 (G), Q10.1 (G), Q11.1 (G), Q12.1 (G), Q13.1 (G), Q18.1 (G), R40.2, R41.1, U6.1
-5V_SW: C53.2, D10.2 (A), Q14.3 (G), Q15.3 (G), Q16.3 (G), Q17.3 (G), R43.2
/Muting Circuit/GND_SW: Q18.3 (D), U5.4 (GND)
CH1_IN: Q6.3 (D); also elsewhere on the board
CH2_IN: Q7.3 (D); also elsewhere on the board
CH3_IN: Q8.3 (D); also elsewhere on the board
CH4_IN: Q9.3 (D); also elsewhere on the board
GND: C45.2, C46.2, C47.1, C48.1, C49.2, C52.1, C53.1, D7.1 (K), J4.2 (GND), J5.2 (GND), J6.2 (GND), J7.2 (GND), Q14.2 (S), Q15.2 (S), Q16.2 (S), Q17.2 (S), Q18.2 (S), R39.1, R43.1, U6.4 (V-), U6.5 (+); also elsewhere on the board
unnamed: C46.1, R36.2, U5.1
unnamed: C49.1, D6.2 (A), R37.2, R40.1, U6.3 (+)
unnamed: C50.1, D7.2 (A), D8.1 (K)
unnamed: C50.2, C51.2, R42.1
unnamed: C51.1, D9.2 (A), D10.1 (K)
unnamed: C52.2, D8.2 (A), D9.1 (K)
unnamed: J4.1 (SIG), Q10.3 (D), Q14.1 (D)
unnamed: J5.1 (SIG), Q11.3 (D), Q15.1 (D)
unnamed: J6.1 (SIG), Q12.3 (D), Q16.1 (D)
unnamed: J7.1 (SIG), Q13.3 (D), Q17.1 (D)
unnamed: Q6.2 (S), Q10.2 (S)
unnamed: Q7.2 (S), Q11.2 (S)
unnamed: Q8.2 (S), Q12.2 (S)
unnamed: Q9.2 (S), Q13.2 (S)
unnamed: R36.1, R42.2, U5.2
unnamed: R38.1, R39.2, U6.2 (_)
unnamed: U5.3, U5.7
unnamed: U5.5, U5.6

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
