freeDSP/freeDSP-CLASSIC-SMD-B/SOURCES/freeDSP_Classic_SMD.kicad_pcb

## KiCad design SOURCES/freeDSP_Classic_SMD.kicad_pcb (continued)

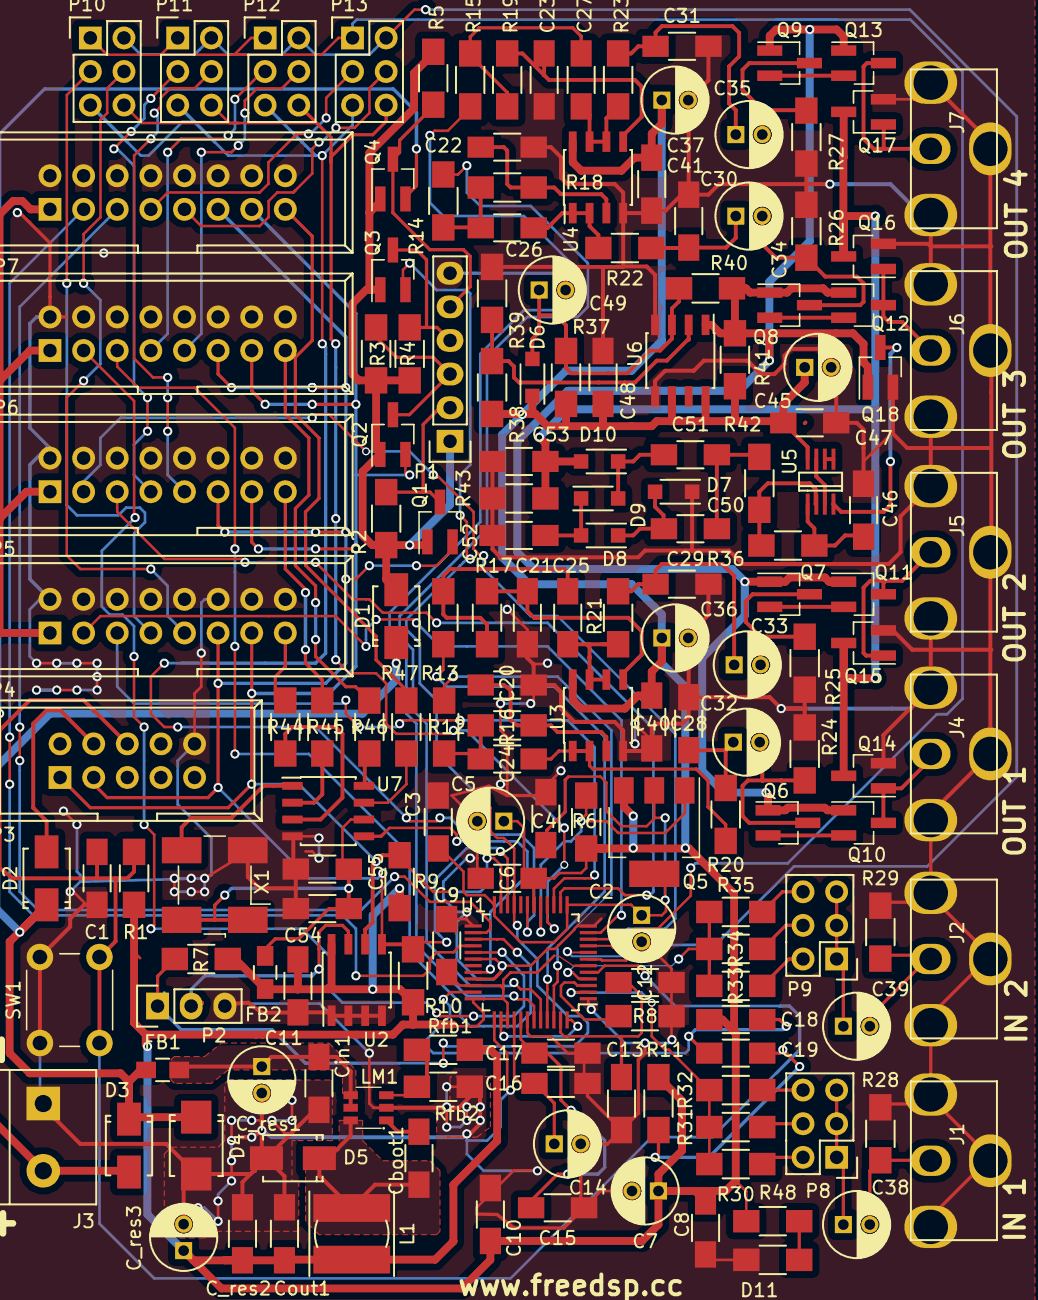
[picture p21: board freeDSP_Classic_SMD.kicad_pcb from above]

Board: 2 copper layers, 170 parts (0 on the bottom side), 116 nets.

Other parts of the board:
C_res1, C_res3: x; C_Radial_D5_L11_P2
C_res2: x; C_1206_HandSoldering
Cboot1: 220n; C_1206_HandSoldering
Cin1: 2u2; C_1206_HandSoldering
Cout1: 47u; C_1206_HandSoldering
D3, D5: B150; SMA
D4: P6SMB 27V; SMB
D11: LED; R_1206_HandSoldering
FB1: 330; C_0805_HandSoldering
J3: CONN_01X02; RIACON101-2
L1: 47u; Choke_SMD_6.0x5.8
LM1: LM284x; SOT23-6_1.7x3.0mm_Pitch0.95mm
P10, P11, P12, P13: CONN_02X03; Pin_Header_Straight_2x03
R48: 330; R_1206_HandSoldering
Rfb1: 3.32k; R_1206_HandSoldering
Rfb2: 1.02k; R_1206_HandSoldering

Their connections:
+12V: D3.2, J3.2; also elsewhere on the board
GND: C_res1.2, C_res2.2, C_res3.2, Cin1.2, Cout1.2, D4.2, D5.2, D11.1, J3.1, LM1.2, Rfb2.2; also elsewhere on the board
MP4: P10.2, P11.2, P12.2, P13.2; also elsewhere on the board
MP5: P10.1, P11.1, P12.1, P13.1; also elsewhere on the board
unnamed: C_res1.1, Cin1.1, FB1.2, LM1.4, LM1.5
unnamed: Cboot1.1, D5.1, L1.1, LM1.6
unnamed: Cboot1.2, LM1.1
unnamed: D11.2, R48.2
unnamed: LM1.3, Rfb1.2, Rfb2.1
VIN: D3.1, D4.1, FB1.1; also elsewhere on the board
